JustinF97/Speedy-Tempomessgeraet/Solidworks/Solidworks_Projektarbeit/Bilder/Rendering_Schild.JPG

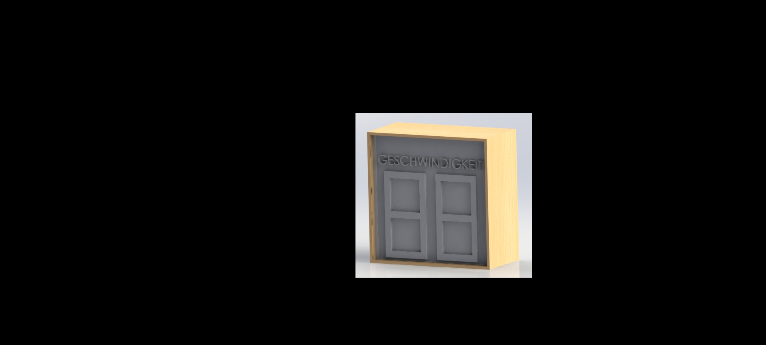
Solidworks/Solidworks_Projektarbeit/Bilder/Rendering_Schild.JPG
